antmicro/jetson-agx-csi-adapter/assets/previews/layer1.png

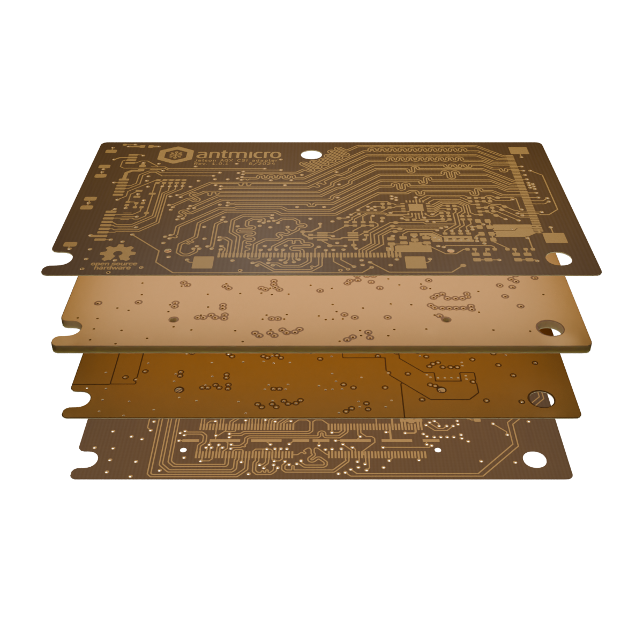
assets/previews/layer1.png
