antmicro/jetson-agx-csi-adapter/assets/previews/layer2.png

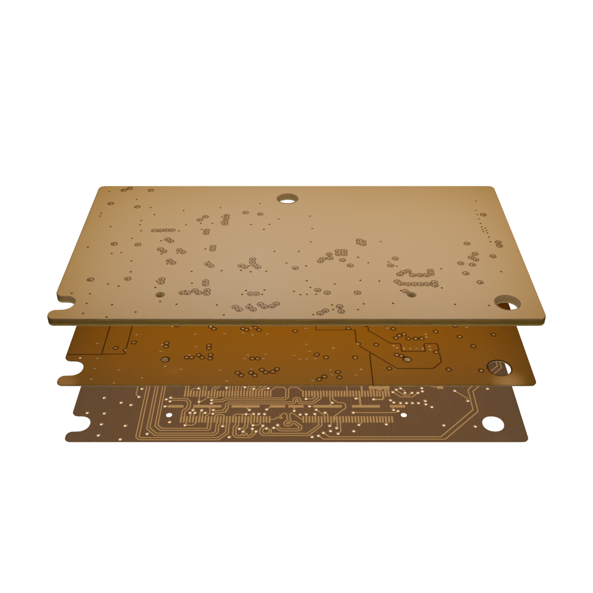
assets/previews/layer2.png
