antmicro/jetson-agx-csi-adapter/assets/previews/layer3.png

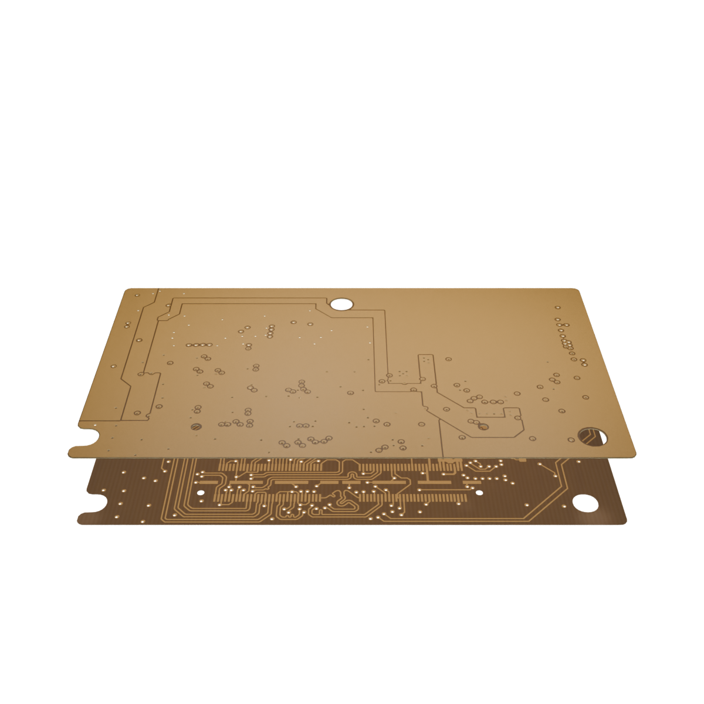
assets/previews/layer3.png
