antmicro/jetson-agx-csi-adapter/assets/previews/layer4.png

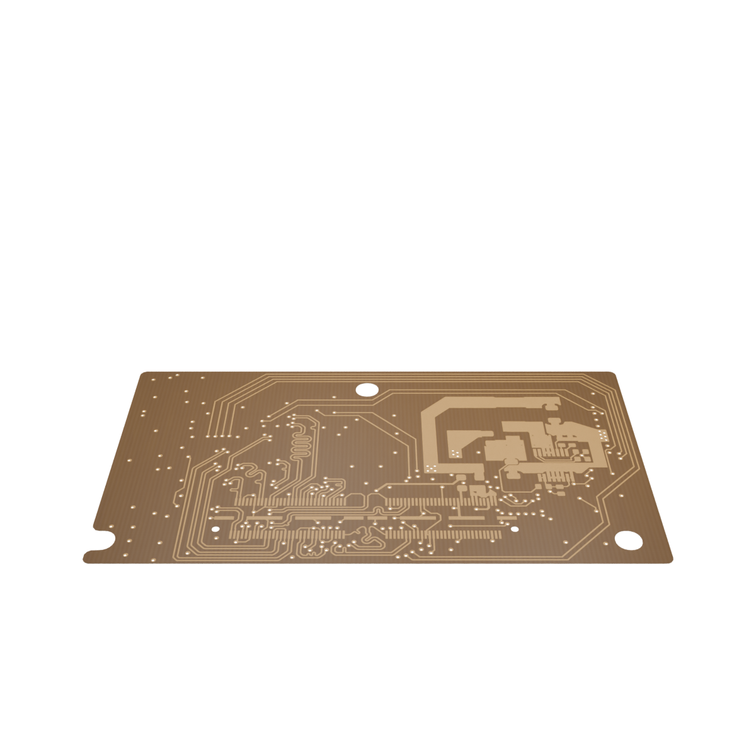
assets/previews/layer4.png
