antmicro/jetson-agx-csi-adapter/assets/previews/leftB.png

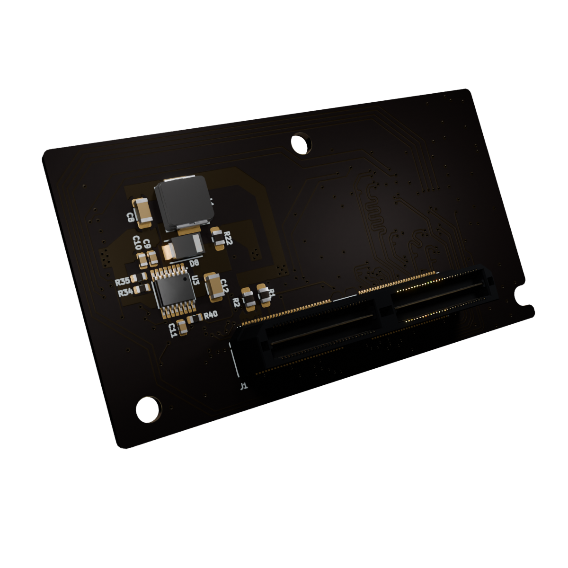
assets/previews/leftB.png
