antmicro/jetson-agx-csi-adapter/assets/previews/leftT.png

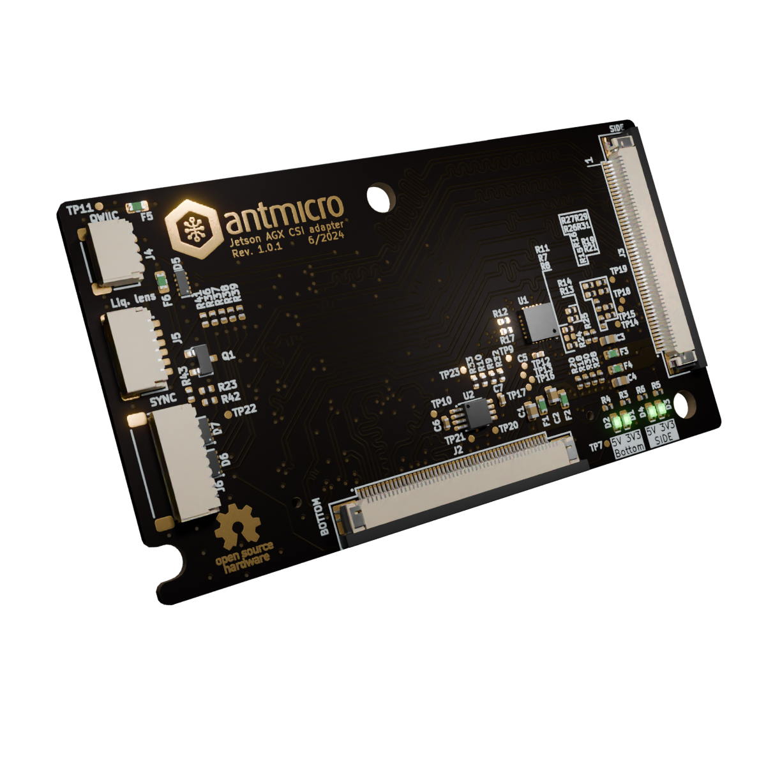
assets/previews/leftT.png
