antmicro/jetson-agx-csi-adapter/assets/previews/orthoB.png

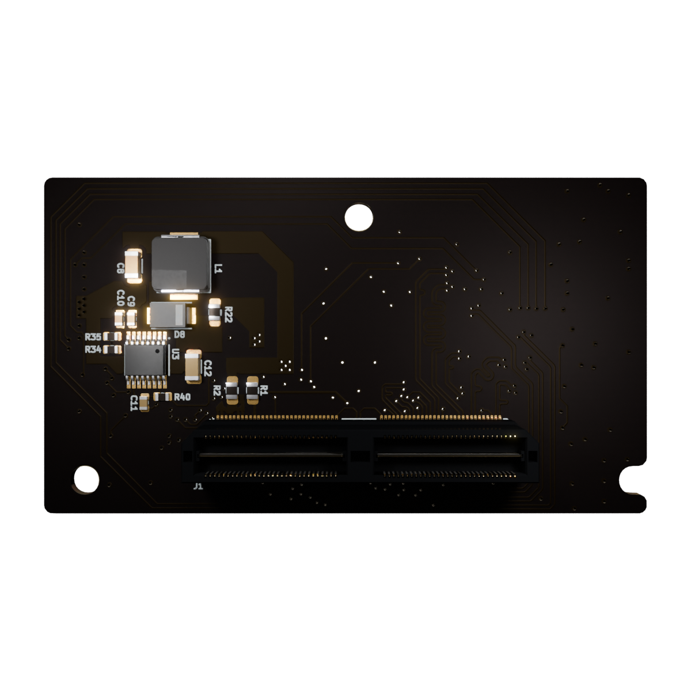
assets/previews/orthoB.png
