antmicro/jetson-agx-csi-adapter/assets/previews/rightB.png

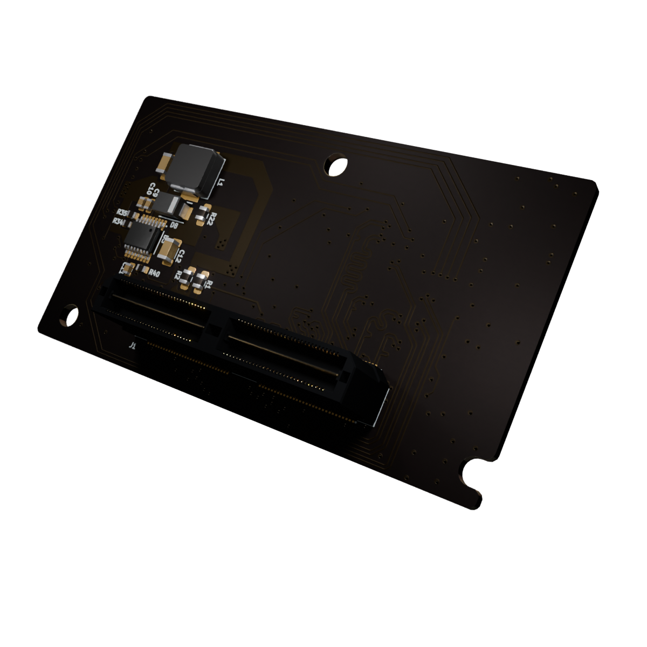
assets/previews/rightB.png
