antmicro/jetson-agx-csi-adapter/assets/previews/rightT.png

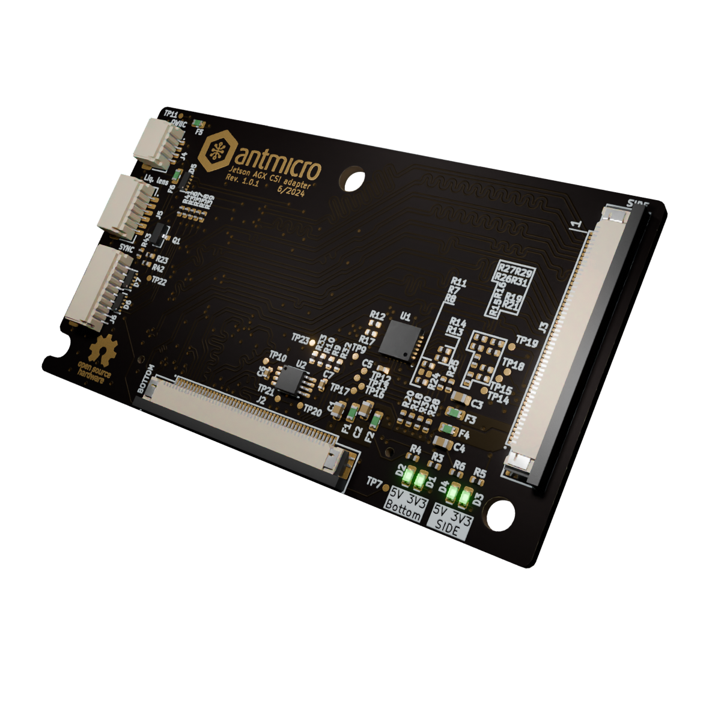
assets/previews/rightT.png
